bsbrl/mini-mScope/Mesoscope CAD Files/082019_mesoscope_frame.SLDPRT

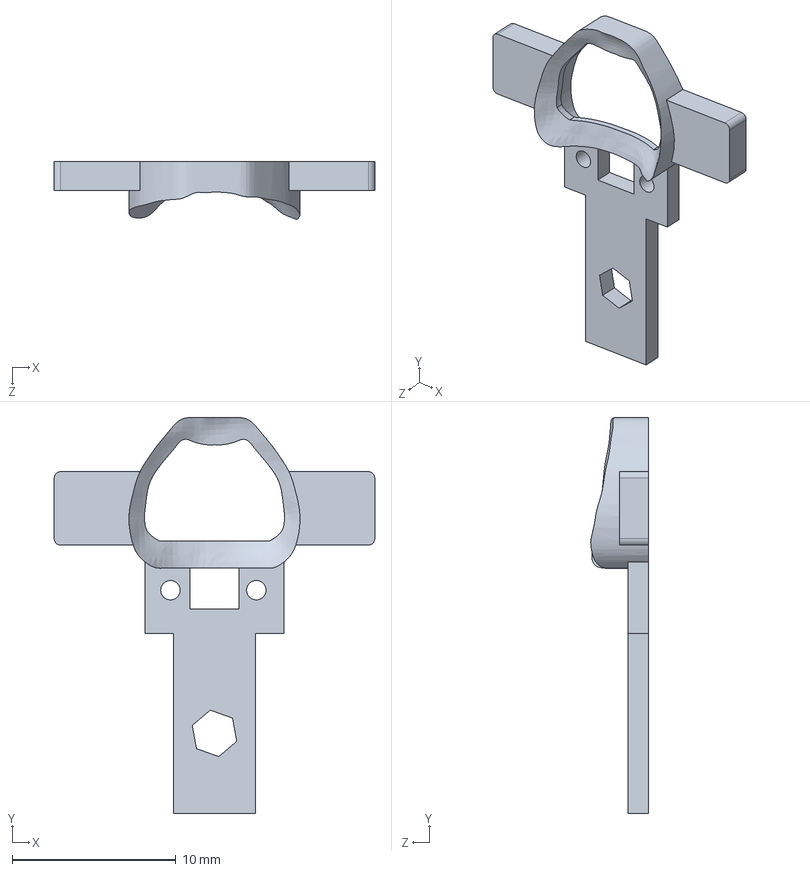
[picture p19: CAD file, 2020-05-29]
Mesoscope CAD Files/082019_mesoscope_frame.SLDPRT
19.6 x 24.2 x 3.52 mm
