bsbrl/mini-mScope/Mesoscope CAD Files/thread_forming_screw.SLDPRT

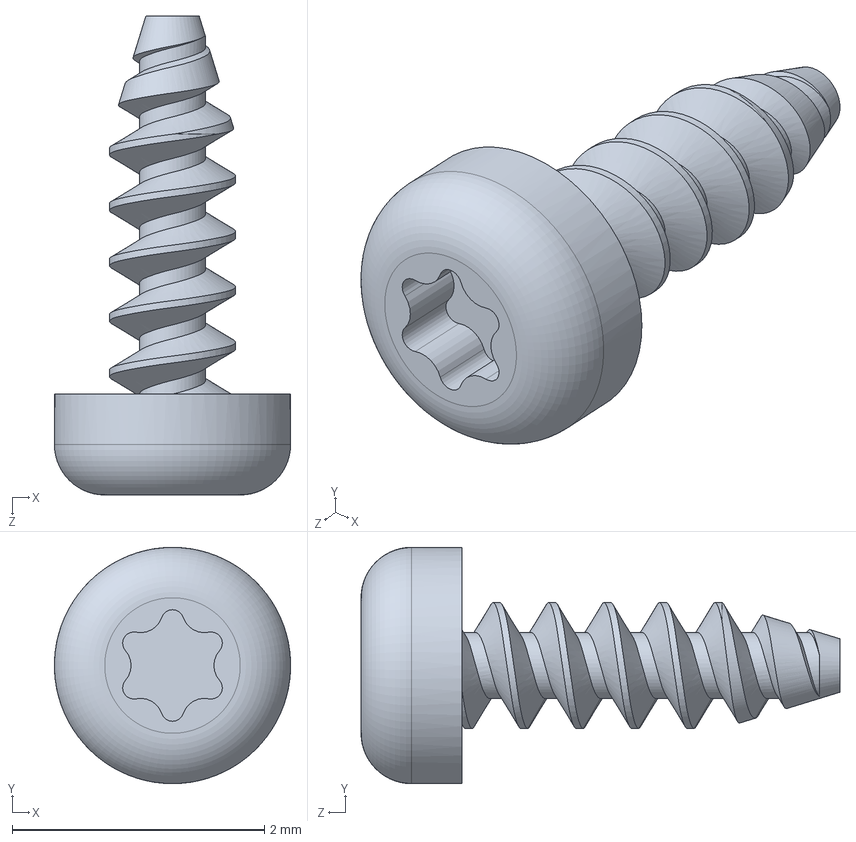
[picture p20: CAD file, 2020-05-29]
Mesoscope CAD Files/thread_forming_screw.SLDPRT
1.88 x 1.88 x 3.80 mm
