bsbrl/mini-mScope/Mesoscope CAD Files/92196A052_18-8 STAINLESS STEEL SOCKET HEAD CAP SCREW.SLDPRT

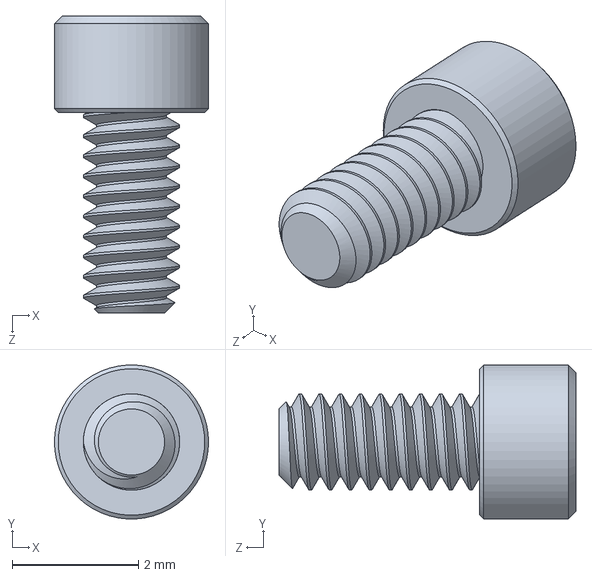
[picture p21: CAD file, 2020-05-29]
Mesoscope CAD Files/92196A052_18-8 STAINLESS STEEL SOCKET HEAD CAP SCREW.SLDPRT
2.44 x 2.43 x 4.70 mm
